rwb27/openflexure_block_stage/docs/images/block_stage_fibre_alignment.jpg

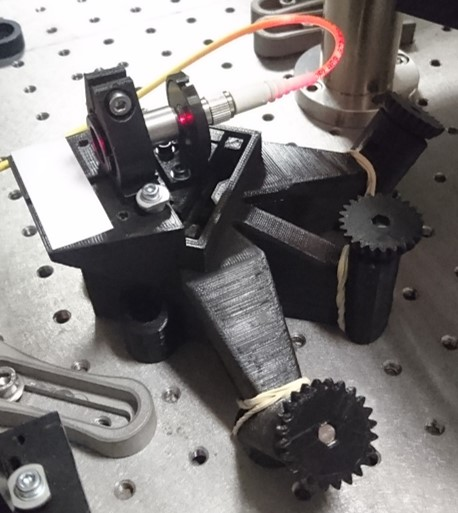
docs/images/block_stage_fibre_alignment.jpg
