rwb27/openflexure_block_stage/docs/Stage Docubricks pic/IMG_20171030_155213.jpg

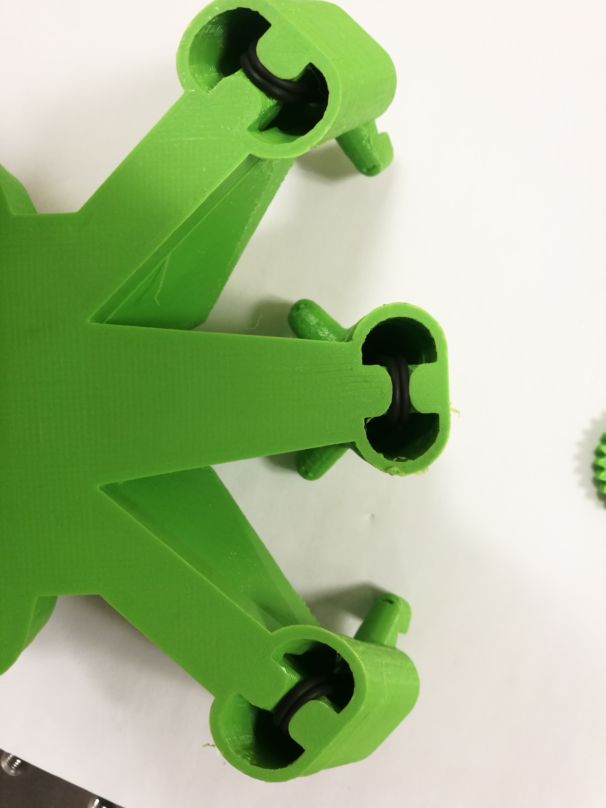
docs/Stage Docubricks pic/IMG_20171030_155213.jpg
