rwb27/openflexure_block_stage/docs/Stage Docubricks pic/IMG_20171031_114917.jpg

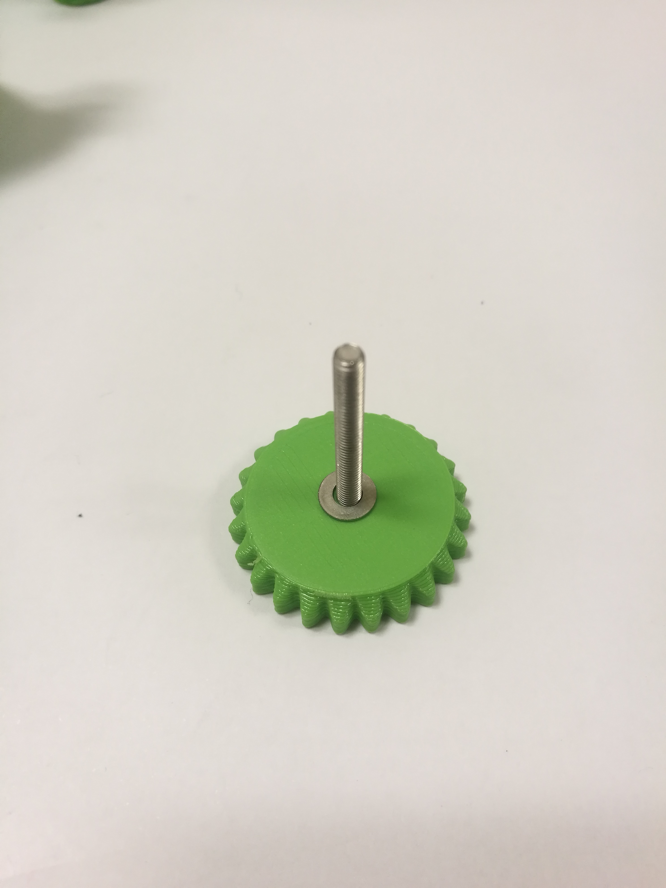
docs/Stage Docubricks pic/IMG_20171031_114917.jpg
