rwb27/openflexure_block_stage/docs/Stage Docubricks pic/IMG_20171113_155440.jpg

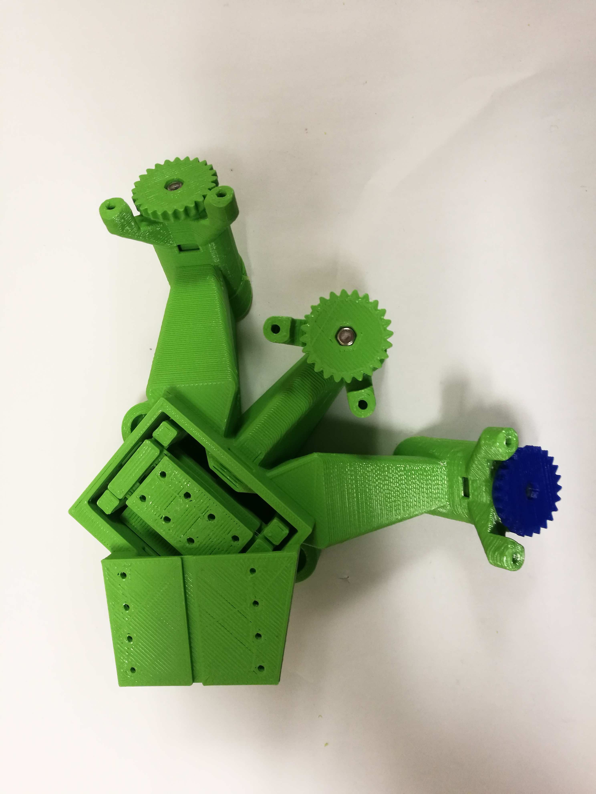
docs/Stage Docubricks pic/IMG_20171113_155440.jpg
