rwb27/openflexure_block_stage/stl/2_fs_body_universal.curaproject.3mf

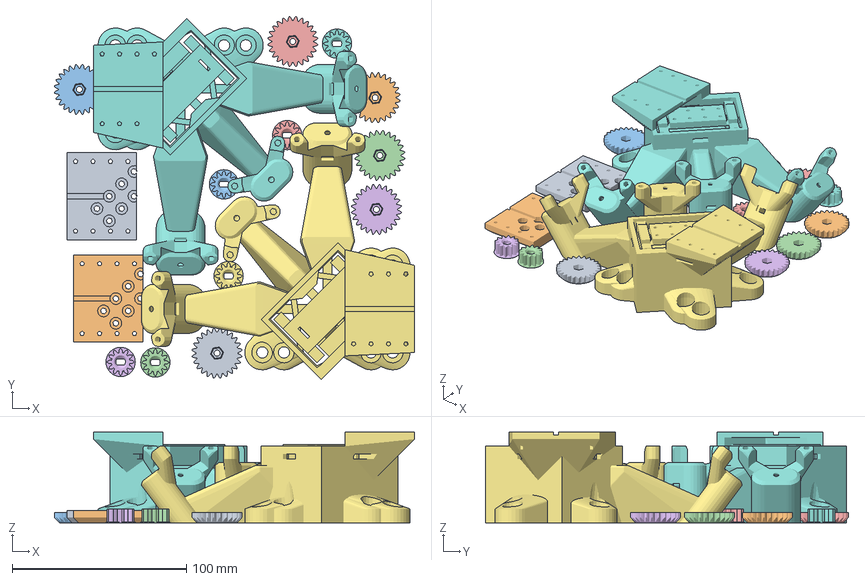
[picture p49: CAD file, 2017-11-27]
stl/2_fs_body_universal.curaproject.3mf
206.6 x 208.1 x 52.0 mm
