rwb27/openflexure_block_stage/stl/accessories/vertical_sample_clips.stl

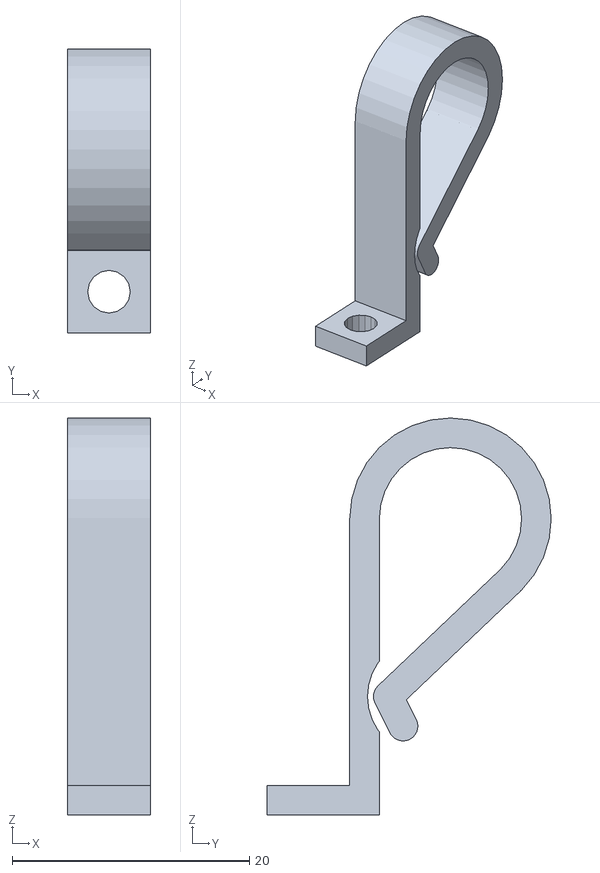
[picture p50: CAD file, 2017-12-11]
stl/accessories/vertical_sample_clips.stl
7.00 x 24.0 x 33.5
