rwb27/openflexure_block_stage/stl/2_fs_body_aligned.curaproject.3mf

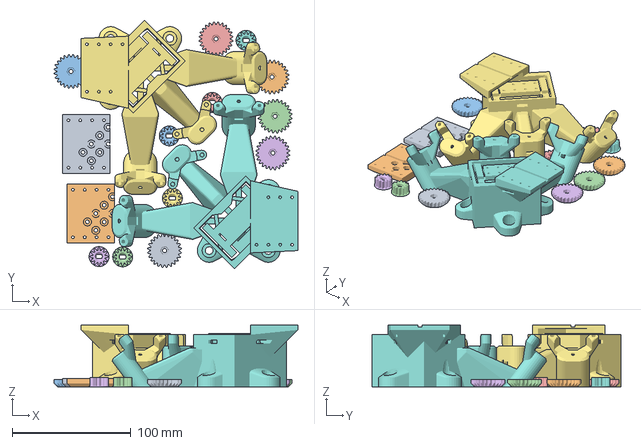
[picture p51: CAD file, 2017-11-27]
stl/2_fs_body_aligned.curaproject.3mf
205.9 x 210.0 x 52.0 mm
