rwb27/openflexure_block_stage/stl/accessories/LED_to_microblock.stl

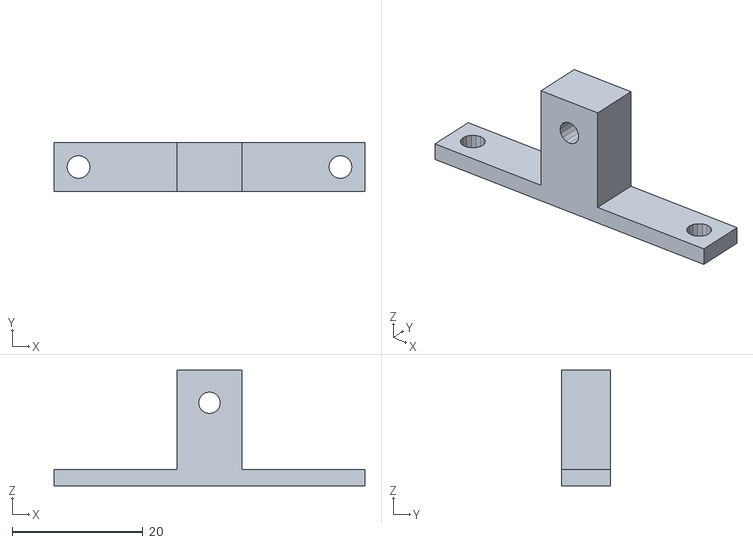
[picture p52: CAD file, 2017-11-24]
stl/accessories/LED_to_microblock.stl
47.5 x 7.50 x 17.7
