rwb27/openflexure_block_stage/stl/2_stages_plus_gears_and_platforms.curaproject.3mf

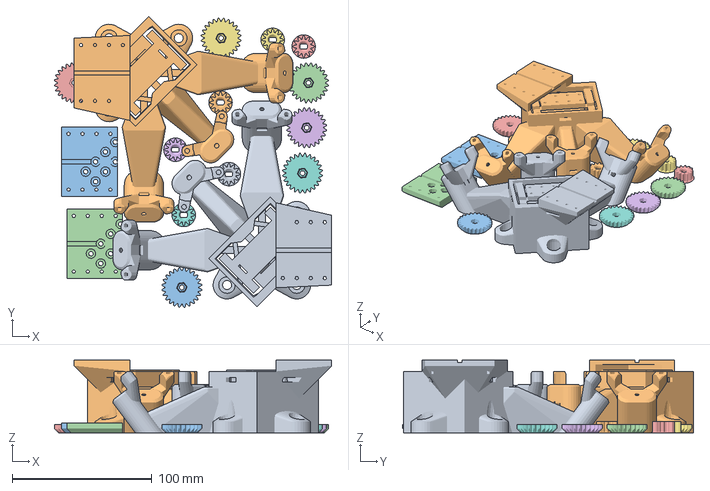
[picture p53: CAD file, 2017-11-24]
stl/2_stages_plus_gears_and_platforms.curaproject.3mf
198.6 x 208.3 x 52.0 mm
