rwb27/openflexure_block_stage/stl/accessories/picam_microscope_60mm.stl

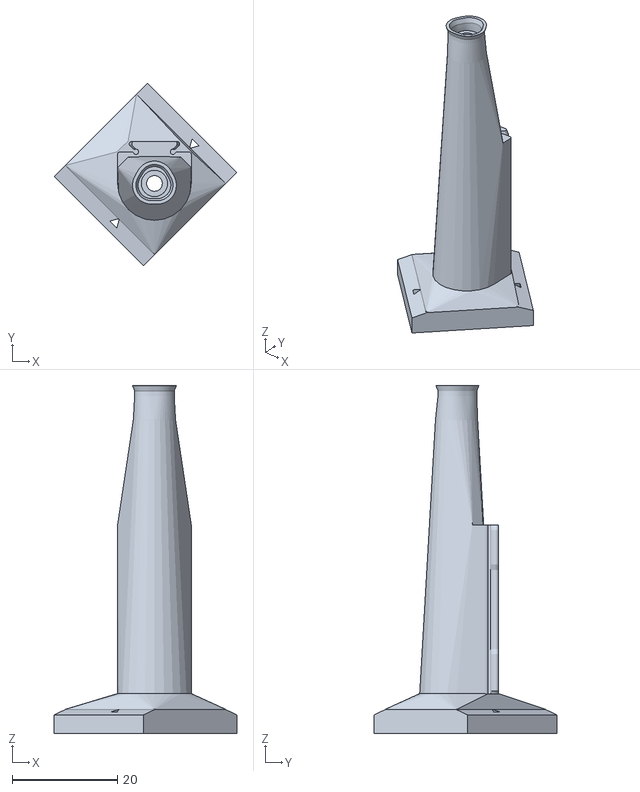
[picture p54: CAD file, 2017-10-20]
stl/accessories/picam_microscope_60mm.stl
34.6 x 34.6 x 66.0
