rwb27/openflexure_block_stage/stl/accessories/openflexure_microscope_adapter.stl

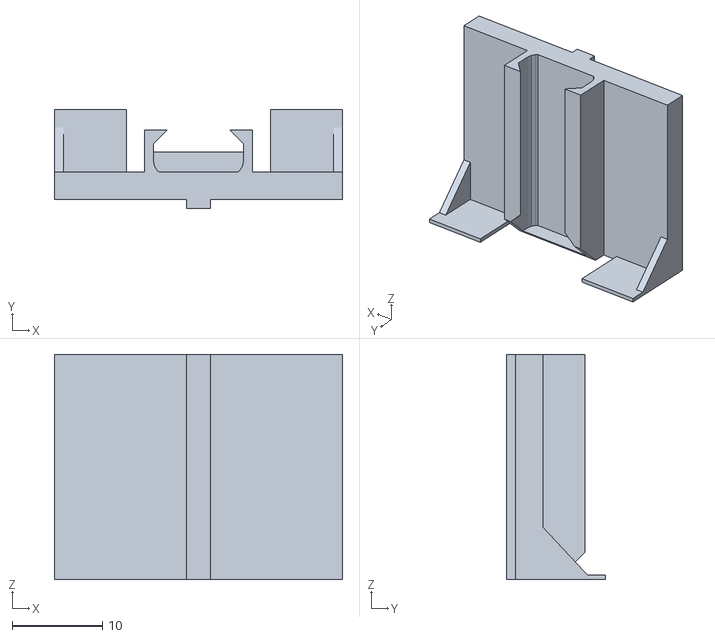
[picture p55: CAD file, 2017-10-20]
stl/accessories/openflexure_microscope_adapter.stl
32.0 x 11.0 x 25.0
