rwb27/openflexure_block_stage/stl/base.stl

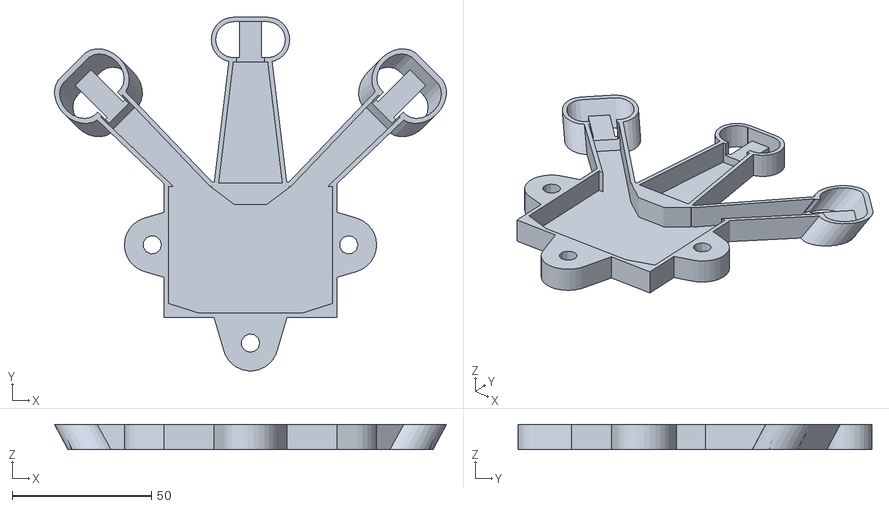
[picture p56: CAD file, 2017-10-03]
stl/base.stl
140.6 x 126.9 x 9.00
