rwb27/openflexure_block_stage/stl/accessories/inch_disc_to_stage.stl

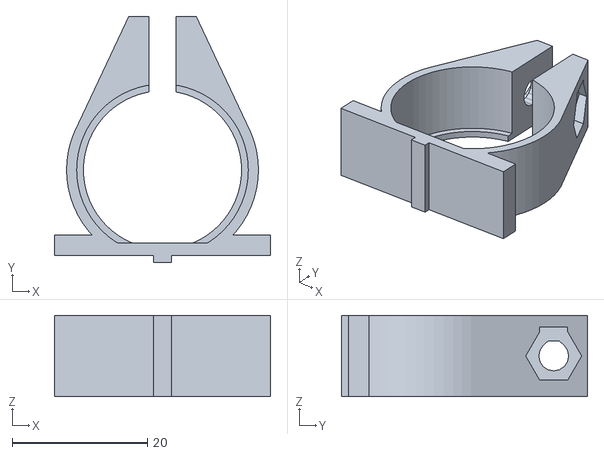
[picture p57: CAD file, 2017-10-03]
stl/accessories/inch_disc_to_stage.stl
32.0 x 36.4 x 12.0
