rwb27/openflexure_block_stage/stl/accessories/inch_disc_adapter.stl

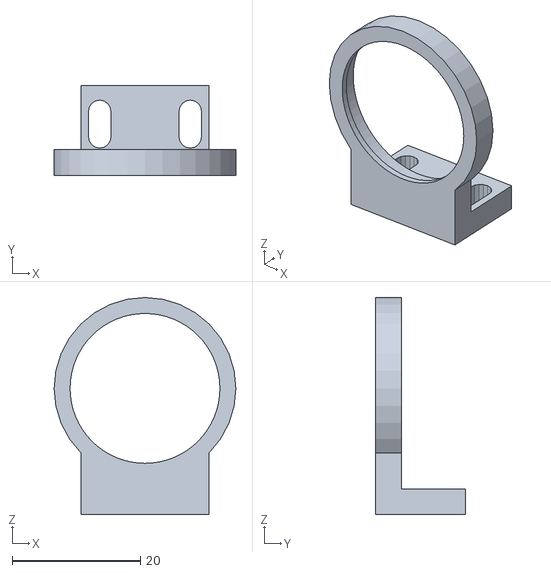
[picture p58: CAD file, 2017-10-03]
stl/accessories/inch_disc_adapter.stl
28.4 x 14.0 x 33.9
