rwb27/openflexure_block_stage/stl/accessories/inch_disc_insertion_tool.stl

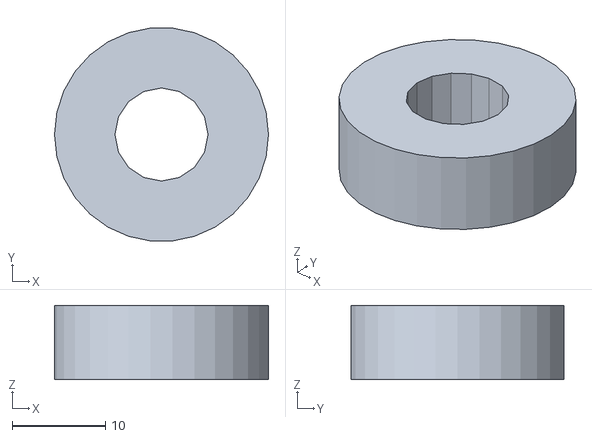
[picture p59: CAD file, 2017-10-03]
stl/accessories/inch_disc_insertion_tool.stl
23.0 x 22.9 x 8.00
