rwb27/openflexure_block_stage/stl/accessories/slide_holder.stl

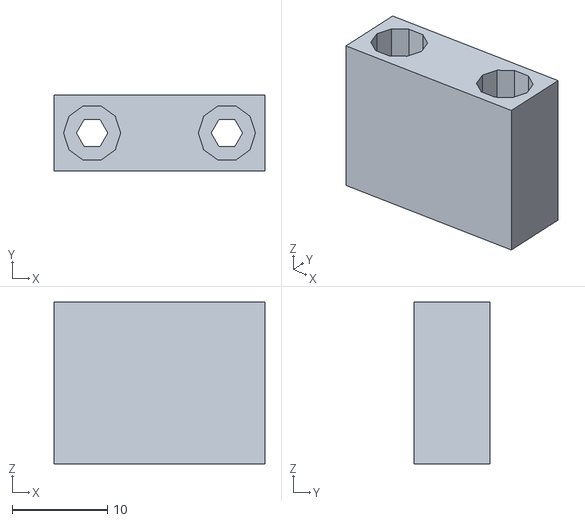
[picture p60: CAD file, 2017-10-03]
stl/accessories/slide_holder.stl
22.1 x 8.00 x 17.0
