rwb27/openflexure_block_stage/stl/accessories/openflexure_microscope_slide_adapter.stl

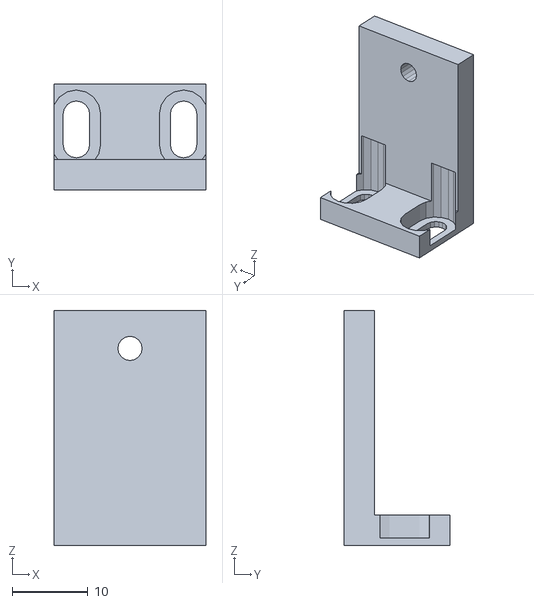
[picture p61: CAD file, 2017-10-03]
stl/accessories/openflexure_microscope_slide_adapter.stl
20.0 x 14.0 x 31.0
