rwb27/openflexure_block_stage/stl/accessories/optics_holder_for_fibre_stage_testing.stl

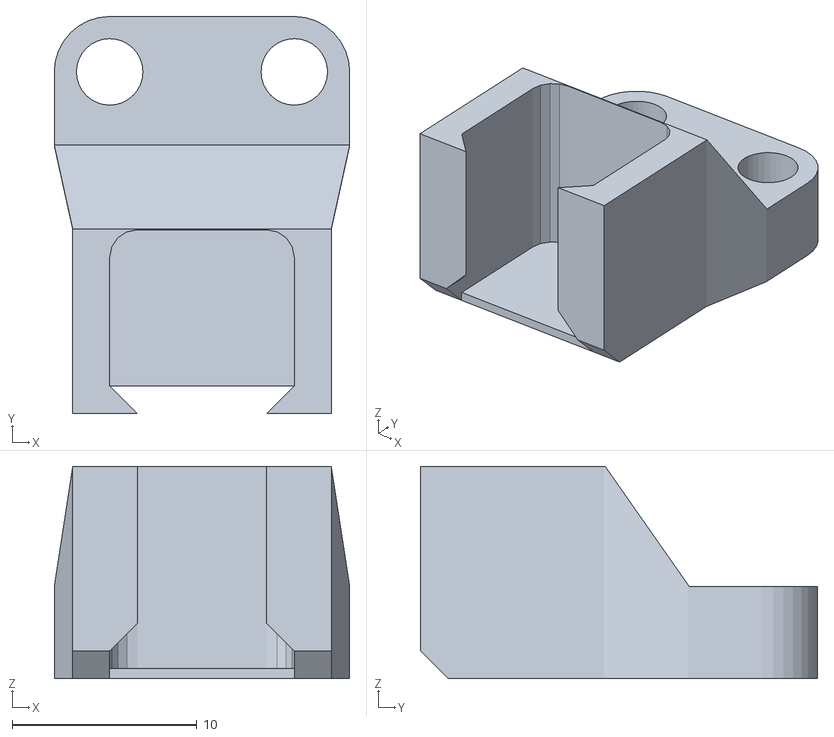
[picture p62: CAD file, 2017-10-03]
stl/accessories/optics_holder_for_fibre_stage_testing.stl
16.0 x 21.5 x 11.5
