rwb27/openflexure_block_stage/openscad/moving_platform.scad

use <fibre_stage_three_legs.scad>;
moving_platform();
