rwb27/openflexure_block_stage/openscad/accessories/microscope_module.scad

/*

An adapter to fit the OpenFlexure Microscope optics module on the
fibre alignment stage

(c) 2016 Richard Bowman - released under CERN Open Hardware License

*/
use <optics_mounts.scad>;

rms_mount_l = 25;
openflexure_microscope_module(rms_mount_l);
